dekuNukem/PulseHPT/resources/photos/lsmodule.jpeg

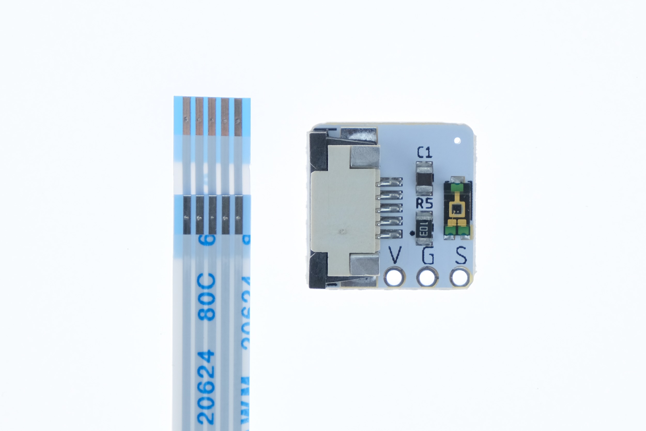
resources/photos/lsmodule.jpeg
