dekuNukem/PulseHPT/resources/photos/my_cable.jpeg

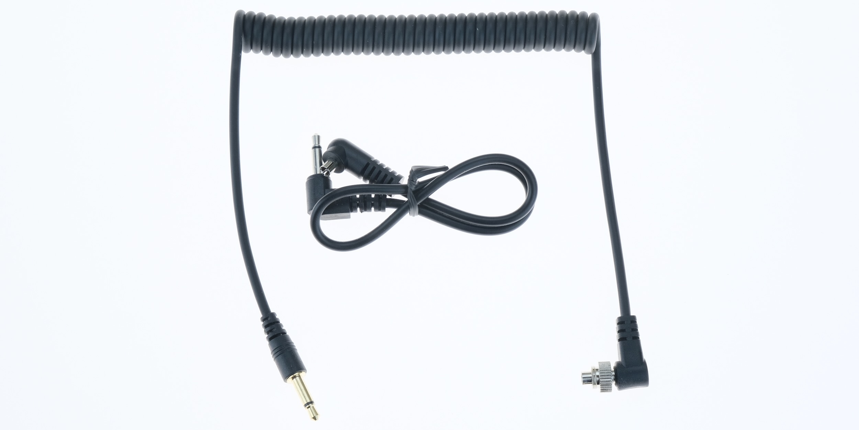
resources/photos/my_cable.jpeg
