dekuNukem/PulseHPT/resources/photos/ttl.jpeg

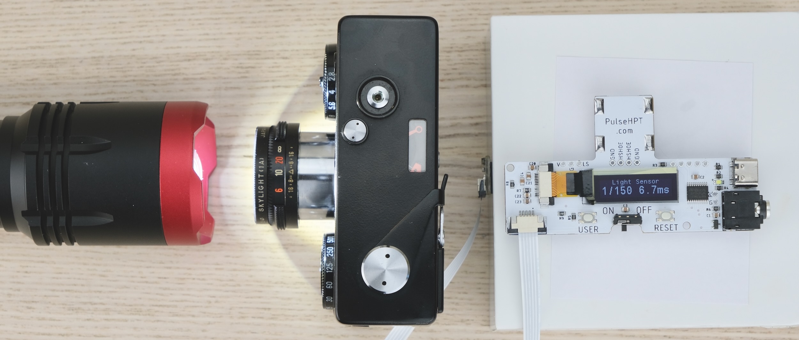
resources/photos/ttl.jpeg
