dekuNukem/PulseHPT/firmware/scraps.c

  // all_ssms[SSM_SOURCE_HOTSHOE].duration = 12345678;
  // all_ssms[SSM_SOURCE_PC].duration = 12345678;
  // all_ssms[SSM_SOURCE_LIGHT_SENSOR].duration = 12345678;
  // print_triple_result();
  all_ssms[0].duration = 16000;
  all_ssms[1].duration = 25000;
  print_double_result("HotShoe", &all_ssms[0], "PC", &all_ssms[1]);
ssd1306_SetContrast(255); is_oled_dim = 0;
Hot Shoe
L Sensor

char* oled_str_device_name = "PulseHPT";

void print_bootscreen(void)
{
  sprintf(temp_str_buf1, "dekuNukem V%d.%d.%d", fw_version_major, fw_version_minor, fw_version_patch);
  ssd1306_Fill(Black);
  ssd1306_SetCursor(center_line(strlen(oled_str_device_name), 11, SSD1306_WIDTH), 0);
  ssd1306_WriteString(oled_str_device_name, Font_11x18, White);
  ssd1306_SetCursor(center_line(strlen(temp_str_buf1), 7, SSD1306_WIDTH), 20);
  ssd1306_WriteString(temp_str_buf1, Font_7x10, White);
  ssd1306_UpdateScreen(); last_oled_update = micros();
}

reset_ssm(&all_ssms[SSM_SOURCE_HOTSHOE]);
  reset_ssm(&all_ssms[SSM_SOURCE_PC]);
  reset_ssm(&all_ssms[SSM_SOURCE_LIGHT_SENSOR]);
    printf("%d %d %d\n", all_ssms[0].current_state, all_ssms[1].current_state, all_ssms[2].current_state);

    uint8_t active_sources = count_active();
    printf("%d\n---\n", active_sources);
    printf("%d %d %d\n", sss_results[SSS_SOURCE_HOTSHOE], sss_results[SSS_SOURCE_PC], sss_results[SSS_SOURCE_LIGHT_SENSOR]);
    printf("%d\n---\n", count_element(sss_results, SSS_SOURCE_SIZE, SHUTTER_STATE_RESULT_AVAILABLE));

    // if(pc_result == SHUTTER_STATE_RESULT_AVAILABLE)
    // {
    //   __disable_irq();
    //   printf("Duration: %ldus\nBounce: %d\n---\n", pc_ssm.duration, pc_ssm.bounce_count);
    //   print_single_result(oled_str_pc_socket, &pc_ssm);
    //   delay_us(200*1000);
    //   reset_ssm(&pc_ssm);
    //   __enable_irq();
    // }
    // else if(pc_result == SHUTTER_STATE_TIMEOUT)
    // {
    //   __disable_irq();
    //   printf("PC TIMEOUT!\n");
    //   delay_us(200*1000);
    //   reset_ssm(&pc_ssm);
    //   __enable_irq();
    // }

    // if(hotshoe_result == SHUTTER_STATE_RESULT_AVAILABLE)
    // {
    //   __disable_irq();
    //   printf("Duration: %ldus\nBounce: %d\n---\n", hotshoe_ssm.duration, hotshoe_ssm.bounce_count);
    //   print_hotshoe(&hotshoe_ssm);
    //   delay_us(200*1000);
    //   reset_ssm(&hotshoe_ssm);
    //   __enable_irq();
    // }
    // else if(hotshoe_result == SHUTTER_STATE_TIMEOUT)
    // {
    //   __disable_irq();
    //   printf("TIMEOUT!\n");
    //   delay_us(200*1000);
    //   reset_ssm(&hotshoe_ssm);
    //   __enable_irq();
    // }
    while(1)
    {
      printf("bye");
      HAL_Delay(2000);
    }

uint8_t center_line(uint8_t line_len, uint8_t char_width_pixels, uint8_t oled_width_pixels)

---
Duration: 37us
Bounce: 2
---
Duration: 324us
Bounce: 6
---
    if(micros() - last_screen_update > 1000*1000)
    {
      ssd1306_SetContrast(8);
    }
uint32_t last_screen_update;
last_screen_update = micros();
last_screen_update = micros();
last_screen_update = micros();

shutter_state_machine test_sss;

  // test_sss.duration = 5;
  // print_hotshoe(&test_sss);
void delay_us(uint32_t delay)
{
  uint32_t end_time = micros() + delay;
  while(micros() < end_time);
}
  while(1)
  {
    // HAL_GPIO_TogglePin(USER_LED_GPIO_Port, USER_LED_Pin);
    USER_LED_GPIO_Port -> BSRR = USER_LED_Pin; // on?
    HAL_Delay(100);
    USER_LED_GPIO_Port -> BRR = USER_LED_Pin;
    HAL_Delay(100);
  }


void print_hotshoe(void) //shutter_state_machine* sss
{
  ssd1306_Fill(Black);
  ssd1306_SetCursor(0, 0);
  ssd1306_WriteString("Hotshoe", Font_7x10, White);
  ssd1306_SetCursor(0, 11);
  ssd1306_WriteString("13.54ms", Font_7x10, White);
  ssd1306_SetCursor(0, 22);
  ssd1306_WriteString("1/44S", Font_7x10, White);

  ssd1306_Line(64,0,64,32,White);

  ssd1306_UpdateScreen();
}

// bounce:

// vvvvvvvvvvv
// 00  0001459796  0001578263
// 01  0001578277  0001578291
// 02  0001578282  0000000000
// 03  0000000000  0000000000
// 04  0000000000  0000000000
// 05  0000000000  0000000000
// 06  0000000000  0000000000
// 07  0000000000  0000000000
// ^^^^^^^^^^^

    // HAL_GPIO_TogglePin(USER_LED_GPIO_Port, USER_LED_Pin);
    // HAL_Delay(1000);


void HAL_GPIO_EXTI_Callback(uint16_t GPIO_Pin)
{
  uint16_t pin_state;
  if(GPIO_Pin == HOTSHOE_Pin)
  {
    pin_state = HOTSHOE_GPIO_Port->IDR & HOTSHOE_Pin;
    // printf("HOTSHOE: %x %d\n", pin_state, micros());
    fill_trigger_log(&hotshoe_thb, pin_state);
  }
  // else if(GPIO_Pin == LIGHT_SENSOR_Pin)
  // {
  //   pin_state = LIGHT_SENSOR_GPIO_Port->IDR & LIGHT_SENSOR_Pin;
  //   printf("LIGHT SENSOR: %x %d\n", pin_state, micros());
  // }
  // else if(GPIO_Pin == PC_SYNC_Pin)
  // {
  //   pin_state = PC_SYNC_GPIO_Port->IDR & PC_SYNC_Pin;
  //   printf("PC SOCKET: %x %d\n", pin_state, micros());
  // }
}





#include <string.h>
#include <stdio.h>
#include "ssd1306.h"
#include "ssd1306_tests.h"

//------------------------------------------------------------------------------
// Table generated by LCD Assistant
// http://en.radzio.dxp.pl/bitmap_converter/
//------------------------------------------------------------------------------
const unsigned char garfield_128x64 [] = {
0x00, 0x00, 0x00, 0x00, 0x00, 0x00, 0x00, 0x00, 0x00, 0x00, 0x00, 0x00, 0x00, 0x00, 0x00, 0x00,
0x00, 0x00, 0x00, 0x00, 0x00, 0x07, 0xFF, 0x00, 0x00, 0x00, 0x00, 0x00, 0x00, 0x00, 0x00, 0x00,
0x00, 0x00, 0x00, 0x00, 0x00, 0x1F, 0xFF, 0xF8, 0x7F, 0xE0, 0x00, 0x00, 0x00, 0x00, 0x00, 0x00,
0x00, 0x00, 0x00, 0x00, 0x00, 0x3F, 0xFF, 0xCF, 0xFF, 0xFE, 0x00, 0x00, 0x00, 0x00, 0x00, 0x00,
0x00, 0x00, 0x00, 0x00, 0x00, 0x3F, 0xFB, 0xE3, 0xFF, 0xF3, 0x80, 0x00, 0x00, 0x00, 0x00, 0x00,
0x00, 0x00, 0x00, 0x00, 0x00, 0x3F, 0xC0, 0xF3, 0xFF, 0xF8, 0xE0, 0x00, 0x00, 0x00, 0x00, 0x00,
0x00, 0x00, 0x00, 0x00, 0x00, 0x1F, 0x00, 0x1F, 0xD9, 0xFC, 0x38, 0x00, 0x00, 0x00, 0x00, 0x00,
0x00, 0x00, 0x00, 0x00, 0x00, 0x0D, 0x00, 0x0F, 0x00, 0x1E, 0x0C, 0x00, 0x00, 0x00, 0x00, 0x00,
0x00, 0x00, 0x00, 0x00, 0x0C, 0x0C, 0x0E, 0x1F, 0xF8, 0x03, 0x04, 0x00, 0x00, 0x00, 0x00, 0x00,
0x00, 0x00, 0x00, 0x00, 0x03, 0x87, 0xF0, 0x07, 0x00, 0x01, 0x86, 0x00, 0x00, 0x00, 0x00, 0x00,
0x00, 0x00, 0x00, 0x00, 0x18, 0x3B, 0x80, 0x18, 0x00, 0x30, 0xC3, 0x00, 0x00, 0x00, 0x00, 0x00,
0x00, 0x00, 0x00, 0x00, 0x00, 0xFE, 0x00, 0x60, 0x00, 0x18, 0xC3, 0x01, 0xC0, 0x00, 0x00, 0x00,
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
0xFF, 0xF0, 0x00, 0x00, 0x00, 0x00, 0x07, 0xFF, 0xFF, 0xF0, 0x00, 0x00, 0x00, 0x00, 0x07, 0xFF,
0xFF, 0xF0, 0x00, 0x00, 0x00, 0x00, 0x0F, 0xFF, 0xFF, 0xF0, 0x00, 0x00, 0x00, 0x00, 0x0F, 0xFF,
0xFF, 0xF0, 0x00, 0x00, 0x00, 0x00, 0x0F, 0xFF, 0xFF, 0xF0, 0x00, 0x00, 0x00, 0x00, 0x0F, 0xFF,
0xFF, 0xF0, 0x00, 0x00, 0x00, 0x00, 0x0F, 0xFF, 0x7F, 0xF8, 0x00, 0x00, 0x00, 0x00, 0x1F, 0xFE,
0x7F, 0xF8, 0x00, 0x00, 0x00, 0x00, 0x1F, 0xFE, 0x7F, 0xFC, 0x00, 0x00, 0x00, 0x00, 0x3F, 0xFE,
0x7F, 0xFC, 0x00, 0x00, 0x00, 0x00, 0x3F, 0xFE, 0x7F, 0xFE, 0x00, 0x00, 0x00, 0x00, 0x7F, 0xFC,
0x3F, 0xFF, 0x00, 0x00, 0x00, 0x00, 0xFF, 0xFC, 0x3F, 0xFF, 0xC0, 0x00, 0x00, 0x01, 0xFF, 0xFC,
0x1F, 0x9F, 0xE0, 0x00, 0x00, 0x07, 0xFF, 0xF8, 0x1F, 0x87, 0xFC, 0x00, 0x00, 0x3F, 0xFF, 0xF8,
0x0F, 0xC3, 0xFF, 0xC0, 0x01, 0xFF, 0xFF, 0xF0, 0x0F, 0xE1, 0xFF, 0x80, 0x01, 0xFF, 0xFF, 0xF0,
0x07, 0xF1, 0xFF, 0x80, 0x00, 0xFF, 0xFF, 0xE0, 0x07, 0xF0, 0xFF, 0x00, 0x00, 0xFF, 0xFF, 0xE0,
0x03, 0xF8, 0x3F, 0x00, 0x00, 0xFF, 0xFF, 0xC0, 0x01, 0xF8, 0x00, 0x00, 0x00, 0xFF, 0xFF, 0x80,
0x00, 0xFC, 0x00, 0x00, 0x00, 0xFF, 0xFF, 0x00, 0x00, 0xFE, 0x00, 0x00, 0x00, 0xFF, 0xFF, 0x00,
0x00, 0x7F, 0x00, 0x00, 0x00, 0xFF, 0xFE, 0x00, 0x00, 0x3F, 0xFF, 0x00, 0x00, 0xFF, 0xFC, 0x00,
0x00, 0x0F, 0xFF, 0x00, 0x00, 0xFF, 0xF0, 0x00, 0x00, 0x07, 0xFF, 0x00, 0x00, 0xFF, 0xE0, 0x00,
0x00, 0x03, 0xFF, 0x00, 0x00, 0xFF, 0xC0, 0x00, 0x00, 0x00, 0xFF, 0x00, 0x00, 0xFF, 0x00, 0x00,
0x00, 0x00, 0x3F, 0x00, 0x00, 0xFC, 0x00, 0x00, 0x00, 0x00, 0x0F, 0x00, 0x00, 0xF0, 0x00, 0x00,
0x00, 0x00, 0x00, 0x00, 0x00, 0x00, 0x00, 0x00, 0x00, 0x00, 0x00, 0x00, 0x00, 0x00, 0x00, 0x00
};

void ssd1306_TestBorder() {
    ssd1306_Fill(Black);
   
    uint8_t x = 0;
    uint8_t y = 0;
    do {
        ssd1306_DrawPixel(x, y, Black);

        if((y == 0) && (x < (SSD1306_WIDTH-1)))
            x++;
        else if((x == (SSD1306_WIDTH-1)) && (y < (SSD1306_HEIGHT-1)))
            y++;
        else if((y == (SSD1306_HEIGHT-1)) && (x > 0)) 
            x--;
        else
            y--;

        ssd1306_DrawPixel(x, y, White);
        ssd1306_UpdateScreen();
    
        HAL_Delay(5);
    } while(x > 0 || y > 0);
   
    HAL_Delay(1000);
}

void ssd1306_TestFonts1() {
    uint8_t y = 0;
    ssd1306_Fill(Black);

    #ifdef SSD1306_INCLUDE_FONT_16x26
    ssd1306_SetCursor(2, y);
    ssd1306_WriteString("Font 16x26", Font_16x26, White);
    y += 26;
    #endif

    #ifdef SSD1306_INCLUDE_FONT_11x18
    ssd1306_SetCursor(2, y);
    ssd1306_WriteString("Font 11x18", Font_11x18, White);
    y += 18;
    #endif

    #ifdef SSD1306_INCLUDE_FONT_7x10
    ssd1306_SetCursor(2, y);
    ssd1306_WriteString("Font 7x10", Font_7x10, White);
    y += 10;
    #endif

    #ifdef SSD1306_INCLUDE_FONT_6x8
    ssd1306_SetCursor(2, y);
    ssd1306_WriteString("Font 6x8", Font_6x8, White);
    #endif

    ssd1306_UpdateScreen();
}

/*
 * This test shows how an 128x64 px OLED can replace a 0802 LCD.
 */
void ssd1306_TestFonts2() {
#ifdef SSD1306_INCLUDE_FONT_16x24
    uint8_t x1, y1, x2, y2;

    ssd1306_Fill(Black);

    ssd1306_SetCursor(0, 4);
    ssd1306_WriteString("18.092.5", Font_16x24, White);
    ssd1306_SetCursor(0, 4+24+8);
    ssd1306_WriteString("RIT+1000", Font_16x24, White);

    // underline
    x1 = 6*16;
    y1 = 4+24+8+24;
    x2 = x1+16;
    y2 = y1+2;
    ssd1306_FillRectangle(x1, y1, x2, y2, White);

    ssd1306_UpdateScreen();
#endif
}

void ssd1306_TestFPS() {
    ssd1306_Fill(White);
   
    uint32_t start = HAL_GetTick();
    uint32_t end = start;
    int fps = 0;
    char message[] = "ABCDEFGHIJK";
   
    ssd1306_SetCursor(2,0);
    ssd1306_WriteString("Testing...", Font_11x18, Black);
    ssd1306_SetCursor(2, 18*2);
    ssd1306_WriteString("0123456789A", Font_11x18, Black);
   
    do {
        ssd1306_SetCursor(2, 18);
        ssd1306_WriteString(message, Font_11x18, Black);
        ssd1306_UpdateScreen();
       
        char ch = message[0];
        memmove(message, message+1, sizeof(message)-2);
        message[sizeof(message)-2] = ch;

        fps++;
        end = HAL_GetTick();
    } while((end - start) < 5000);
   
    HAL_Delay(5000);

    char buff[64];
    fps = (float)fps / ((end - start) / 1000.0);
    snprintf(buff, sizeof(buff), "~%d FPS", fps);
   
    ssd1306_Fill(White);
    ssd1306_SetCursor(2, 2);
    ssd1306_WriteString(buff, Font_11x18, Black);
    ssd1306_UpdateScreen();
}

void ssd1306_TestLine() {

  ssd1306_Line(1,1,SSD1306_WIDTH - 1,SSD1306_HEIGHT - 1,White);
  ssd1306_Line(SSD1306_WIDTH - 1,1,1,SSD1306_HEIGHT - 1,White);
  ssd1306_UpdateScreen();
  return;
}

void ssd1306_TestRectangle() {
  uint32_t delta;

  for(delta = 0; delta < 5; delta ++) {
    ssd1306_DrawRectangle(1 + (5*delta),1 + (5*delta) ,SSD1306_WIDTH-1 - (5*delta),SSD1306_HEIGHT-1 - (5*delta),White);
  }
  ssd1306_UpdateScreen();
  return;
}

void ssd1306_TestRectangleFill() {
  ssd1306_FillRectangle(31, 1, 65, 35, White);
  ssd1306_FillRectangle(10, 45, 70, 60, White);
  ssd1306_FillRectangle(75, 10, 100, 45, White);
  ssd1306_FillRectangle(55, 30, 80, 55, Black);
  ssd1306_UpdateScreen();
}

void ssd1306_TestCircle() {
  uint32_t delta;

  for(delta = 0; delta < 5; delta ++) {
    ssd1306_DrawCircle(20*delta+30, 15, 10, White);
  }

  for(delta = 0; delta < 5; delta ++) {
    ssd1306_FillCircle(23*delta+15, 40, 10, White);
  }

  ssd1306_UpdateScreen();
  return;
}

void ssd1306_TestArc() {
  ssd1306_DrawArc(30, 30, 30, 20, 270, White);
  ssd1306_DrawArcWithRadiusLine(80, 55, 10, 30, 270, White);
  ssd1306_UpdateScreen();
  return;
}

void ssd1306_TestPolyline() {
  SSD1306_VERTEX loc_vertex[] =
  {
      {35,40},
      {40,20},
      {45,28},
      {50,10},
      {45,16},
      {50,10},
      {53,16}
  };

  ssd1306_Polyline(loc_vertex,sizeof(loc_vertex)/sizeof(loc_vertex[0]),White);
  ssd1306_UpdateScreen();
  return;
}

void ssd1306_TestDrawBitmap()
{
    ssd1306_Fill(White);
    ssd1306_DrawBitmap(0,0,garfield_128x64,128,64,Black);
    ssd1306_UpdateScreen();
    HAL_Delay(3000);
    ssd1306_Fill(Black);
    ssd1306_DrawBitmap(32,0,github_logo_64x64,64,64,White);
    ssd1306_UpdateScreen();
    HAL_Delay(3000);
    ssd1306_Fill(White);
    ssd1306_DrawBitmap(32,0,github_logo_64x64,64,64,Black);
    ssd1306_UpdateScreen();
}

void ssd1306_TestAll() {
    ssd1306_Init();

    ssd1306_TestFPS();
    HAL_Delay(3000);
    ssd1306_TestBorder();
    ssd1306_TestFonts1();
    HAL_Delay(3000);
    ssd1306_TestFonts2();
    HAL_Delay(3000);
    ssd1306_Fill(Black);
    ssd1306_TestRectangle();
    ssd1306_TestLine();
    HAL_Delay(3000);
    ssd1306_Fill(Black);
    ssd1306_TestRectangleFill();
    HAL_Delay(3000);
    ssd1306_Fill(Black);
    ssd1306_TestPolyline();
    HAL_Delay(3000);
    ssd1306_Fill(Black);
    ssd1306_TestArc();
    HAL_Delay(3000);
    ssd1306_Fill(Black);
    ssd1306_TestCircle();
    HAL_Delay(3000);
    ssd1306_TestDrawBitmap();
    HAL_Delay(3000);
}
